dimaib/Pulse_bracelet/braslet/schematic&pcb/Корпуса/Корпус_103new/плата.SLDPRT

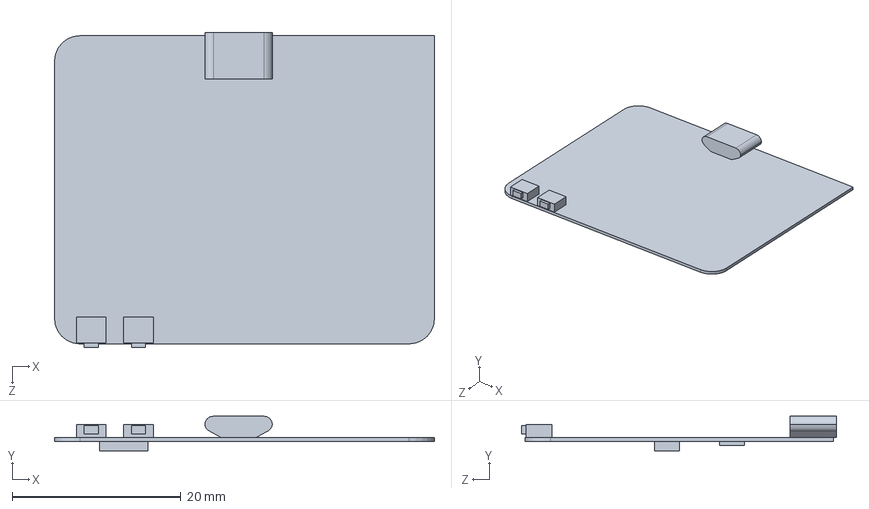
[picture p17: CAD file, 2022-04-17]
braslet/schematic&pcb/Корпуса/Корпус_103new/плата.SLDPRT
45.0 x 4.10 x 37.2 mm
