dimaib/Pulse_bracelet/Prog/body_temp_103new_optimized/Inc/hello.h

#ifndef HELLO_H
#define HELLO_H
#include "main.h"

//uint32_t foo_size=4364;

char foo[] = {
  0x80, 0x7f, 0x80, 0x7f, 0x80, 0x7f, 0x80, 0x7f, 
  0x80, 0x7f, 0x80, 0x7f, 0x80, 0x80, 0x80, 0x81, 
  0x81, 0x80, 0x81, 0x81, 0x7f, 0x80, 0x80, 0x80, 
  0x80, 0x7f, 0x80, 0x80, 0x7f, 0x7f, 0x7f, 0x7f, 
  0x7f, 0x7e, 0x7f, 0x7f, 0x7f, 0x7f, 0x80, 0x80, 
  0x80, 0x80, 0x7f, 0x81, 0x80, 0x81, 0x81, 0x80, 
  0x80, 0x80, 0x82, 0x82, 0x80, 0x80, 0x7f, 0x80, 
  0x7f, 0x7e, 0x7e, 0x7d, 0x7e, 0x7e, 0x7e, 0x7d, 
  0x7c, 0x7d, 0x7e, 0x7f, 0x7e, 0x7f, 0x7f, 0x80, 
  0x7f, 0x80, 0x80, 0x80, 0x80, 0x7f, 0x80, 0x7f, 
  0x7e, 0x7f, 0x7e, 0x7c, 0x7e, 0x7f, 0x7e, 0x7d, 
  0x7c, 0x7e, 0x7e, 0x7d, 0x7c, 0x7d, 0x7d, 0x7d, 
  0x7c, 0x7d, 0x7d, 0x7d, 0x7e, 0x80, 0x82, 0x84, 
  0x86, 0x87, 0x89, 0x8b, 0x8a, 0x89, 0x88, 0x86, 
  0x84, 0x80, 0x7e, 0x7e, 0x7b, 0x79, 0x79, 0x79, 
  0x7a, 0x7a, 0x7b, 0x7b, 0x7c, 0x7b, 0x7c, 0x7c, 
  0x7a, 0x7a, 0x79, 0x79, 0x79, 0x7a, 0x79, 0x7a, 
  0x7f, 0x85, 0x88, 0x8a, 0x90, 0x94, 0x96, 0x94, 
  0x91, 0x91, 0x8c, 0x85, 0x81, 0x7b, 0x78, 0x74, 
  0x71, 0x72, 0x72, 0x76, 0x77, 0x78, 0x7c, 0x7c, 
  0x7d, 0x7d, 0x7b, 0x7a, 0x79, 0x77, 0x76, 0x75, 
  0x75, 0x76, 0x76, 0x7d, 0x88, 0x89, 0x8e, 0x98, 
  0x9b, 0x9e, 0x9c, 0x98, 0x96, 0x8f, 0x84, 0x7e, 
  0x77, 0x71, 0x6d, 0x6b, 0x6c, 0x6e, 0x73, 0x76, 
  0x7b, 0x7d, 0x7f, 0x80, 0x7f, 0x7f, 0x7c, 0x7a, 
  0x77, 0x75, 0x73, 0x73, 0x74, 0x73, 0x7c, 0x88, 
  0x88, 0x8f, 0x9a, 0x9d, 0x9f, 0x9e, 0x9a, 0x99, 
  0x90, 0x85, 0x7f, 0x78, 0x70, 0x6d, 0x6a, 0x6b, 
  0x6e, 0x71, 0x76, 0x7a, 0x7c, 0x7f, 0x7f, 0x7f, 
  0x7e, 0x7b, 0x7a, 0x76, 0x75, 0x74, 0x73, 0x74, 
  0x73, 0x7b, 0x85, 0x85, 0x8c, 0x97, 0x99, 0x9c, 
  0x9c, 0x9a, 0x99, 0x92, 0x89, 0x84, 0x7e, 0x77, 
  0x73, 0x70, 0x70, 0x6f, 0x71, 0x74, 0x75, 0x78, 
  0x79, 0x7b, 0x7c, 0x79, 0x79, 0x78, 0x76, 0x76, 
  0x74, 0x75, 0x76, 0x74, 0x7a, 0x81, 0x83, 0x88, 
  0x8f, 0x95, 0x97, 0x97, 0x98, 0x98, 0x93, 0x8e, 
  0x89, 0x84, 0x80, 0x7b, 0x79, 0x78, 0x76, 0x77, 
  0x76, 0x78, 0x78, 0x78, 0x79, 0x79, 0x79, 0x77, 
  0x77, 0x77, 0x76, 0x76, 0x76, 0x76, 0x76, 0x77, 
  0x7c, 0x80, 0x83, 0x87, 0x8c, 0x8f, 0x91, 0x91, 
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
};

#endif	//HELLO_H
