dimaib/Pulse_bracelet/Prog/body_temp_103new_optimized/Inc/wav_arr.h

static const char wav_ism_puls[] = {
  0x80, 0x7f, 0x7f, 0x7e, 0x7f, 0x80, 0x80, 0x7f, 
  0x80, 0x81, 0x81, 0x81, 0x82, 0x83, 0x82, 0x82, 
  0x83, 0x84, 0x83, 0x82, 0x82, 0x81, 0x80, 0x81, 
  0x80, 0x7f, 0x80, 0x7f, 0x80, 0x7f, 0x7f, 0x7f, 
  0x7f, 0x7f, 0x7f, 0x7e, 0x7f, 0x7f, 0x7f, 0x7f, 
  0x7e, 0x7f, 0x7e, 0x7f, 0x7e, 0x7f, 0x7e, 0x7f, 
  0x7f, 0x7f, 0x7f, 0x7e, 0x7f, 0x7e, 0x7f, 0x7e, 
  0x7e, 0x7f, 0x7e, 0x7e, 0x7f, 0x7e, 0x7f, 0x7e, 
  0x7e, 0x7f, 0x7e, 0x7f, 0x7e, 0x7d, 0x7e, 0x7e, 
  0x7f, 0x7f, 0x80, 0x81, 0x82, 0x82, 0x83, 0x83, 
  0x84, 0x85, 0x86, 0x85, 0x86, 0x85, 0x84, 0x84, 
  0x84, 0x83, 0x83, 0x82, 0x82, 0x81, 0x80, 0x80, 
  0x80, 0x80, 0x80, 0x80, 0x7f, 0x80, 0x7f, 0x80, 
  0x7f, 0x7e, 0x7f, 0x7e, 0x7f, 0x7e, 0x7e, 0x7d, 
  0x7e, 0x7d, 0x7e, 0x7d, 0x7d, 0x7e, 0x7d, 0x7d, 
  0x7d, 0x7c, 0x7d, 0x7c, 0x7d, 0x7d, 0x7c, 0x7d, 
  0x7c, 0x7d, 0x7c, 0x7d, 0x7d, 0x7c, 0x7c, 0x7c, 
  0x7c, 0x7c, 0x7c, 0x7b, 0x7c, 0x7d, 0x7f, 0x80, 
  0x80, 0x81, 0x82, 0x83, 0x84, 0x85, 0x86, 0x87, 
  0x88, 0x88, 0x87, 0x87, 0x86, 0x86, 0x86, 0x86, 
  0x85, 0x85, 0x84, 0x84, 0x83, 0x82, 0x82, 0x82, 
  0x82, 0x81, 0x81, 0x80, 0x7f, 0x80, 0x7f, 0x80, 
  0x7f, 0x7e, 0x7e, 0x7e, 0x7e, 0x7d, 0x7d, 0x7d, 
  0x7c, 0x7d, 0x7c, 0x7c, 0x7b, 0x7c, 0x7b, 0x7b, 
  0x7b, 0x7b, 0x7b, 0x7b, 0x7a, 0x7b, 0x7a, 0x7b, 
  0x7a, 0x7b, 0x7b, 0x7a, 0x7a, 0x7a, 0x7a, 0x7a, 
  0x79, 0x7a, 0x7a, 0x7b, 0x7c, 0x7e, 0x7f, 0x80, 
  0x80, 0x81, 0x83, 0x84, 0x86, 0x87, 0x88, 0x88, 
  0x89, 0x88, 0x89, 0x89, 0x89, 0x88, 0x89, 0x88, 
  0x88, 0x87, 0x87, 0x86, 0x86, 0x85, 0x84, 0x84, 
  0x83, 0x83, 0x82, 0x81, 0x81, 0x80, 0x80, 0x7f, 
  0x80, 0x7f, 0x7f, 0x7e, 0x7e, 0x7e, 0x7c, 0x7d, 
  0x7c, 0x7b, 0x7c, 0x7b, 0x7b, 0x7b, 0x7a, 0x7b, 
  0x7a, 0x7a, 0x7a, 0x79, 0x7a, 0x79, 0x79, 0x79, 
  0x79, 0x79, 0x79, 0x78, 0x79, 0x78, 0x79, 0x78, 
  0x79, 0x78, 0x79, 0x7a, 0x7c, 0x7e, 0x7f, 0x7f, 
  0x80, 0x81, 0x82, 0x84, 0x86, 0x87, 0x88, 0x88, 
  0x89, 0x88, 0x89, 0x8a, 0x89, 0x8a, 0x89, 0x89, 
  0x89, 0x88, 0x87, 0x87, 0x86, 0x86, 0x85, 0x84, 
  0x84, 0x83, 0x82, 0x81, 0x81, 0x80, 0x80, 0x7f, 
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
};
