dimaib/Pulse_bracelet/Prog/body_temp_103new_optimized/Inc/spx.h

#include "main.h"

#ifndef SPX_H
#define SPX_H
unsigned int spx_size=1248;
const uint16_t spx_frames2=62;

const uint8_t spx_voice2[] = {
  0x88, 0x0e, 0x73, 0x9d, 0xb4, 0x07, 0x39, 0xce, 
  0x1e, 0x9d, 0x66, 0x0f, 0xc0, 0x39, 0xce, 0x70, 
  0x00, 0x1c, 0xe7, 0x38, 0x10, 0x0e, 0x73, 0x9c, 
  0x00, 0x07, 0x39, 0xce, 0x1e, 0x9d, 0x66, 0x00, 
  0x00, 0x39, 0xce, 0x70, 0x00, 0x1c, 0xe7, 0x38, 
  0x00, 0x0e, 0x73, 0x9c, 0x00, 0x07, 0x39, 0xce, 
  0x1e, 0x9d, 0x66, 0x00, 0x00, 0x39, 0xce, 0x70, 
  0x00, 0x1c, 0xe7, 0x38, 0x00, 0x0e, 0x73, 0x9c, 
  0x00, 0x07, 0x39, 0xce, 0x1e, 0x9d, 0x66, 0x00, 
  0x00, 0x39, 0xce, 0x70, 0x00, 0x1c, 0xe7, 0x38, 
  0x00, 0x0e, 0x73, 0x9c, 0x00, 0x07, 0x39, 0xce, 
  0x1e, 0x9d, 0x66, 0x00, 0x00, 0x39, 0xce, 0x70, 
  0x00, 0x1c, 0xe7, 0x38, 0x00, 0x0e, 0x73, 0x9c, 
  0x00, 0x07, 0x39, 0xce, 0x1e, 0x9d, 0x66, 0x00, 
  0x00, 0x39, 0xce, 0x70, 0x00, 0x1c, 0xe7, 0x38, 
  0x00, 0x0e, 0x73, 0x9c, 0x00, 0x07, 0x39, 0xce, 
  0x1e, 0x9d, 0x66, 0x00, 0x00, 0x39, 0xce, 0x70, 
  0x00, 0x1c, 0xe7, 0x38, 0x00, 0x0e, 0x73, 0x9c, 
  0x00, 0x07, 0x39, 0xce, 0x1e, 0x9d, 0x66, 0x00, 
  0x00, 0x39, 0xce, 0x70, 0x00, 0x1c, 0xe7, 0x38, 
  0x00, 0x0e, 0x73, 0x9c, 0x00, 0x07, 0x39, 0xce, 
  0x1e, 0x9d, 0x66, 0x00, 0x00, 0x39, 0xce, 0x70, 
  0x00, 0x1c, 0xe7, 0x38, 0x00, 0x0e, 0x73, 0x9c, 
  0x00, 0x07, 0x39, 0xce, 0x1c, 0x5f, 0xa8, 0x80, 
  0x40, 0x39, 0xce, 0x70, 0x90, 0x1c, 0xe7, 0x24, 
  0xbc, 0x9e, 0x55, 0xc4, 0x32, 0x19, 0x80, 0x16, 
  0x1c, 0x49, 0x43, 0x34, 0xb0, 0x3b, 0x90, 0xc8, 
  0xd8, 0x06, 0x5e, 0xa0, 0x67, 0x74, 0x6c, 0x98, 
  0xa2, 0x54, 0xdf, 0x78, 0x1c, 0x4c, 0x63, 0x71, 
  0x74, 0x37, 0x91, 0x70, 0xad, 0xda, 0xea, 0x38, 
  0x55, 0x81, 0xdb, 0xfc, 0x27, 0xbd, 0x4a, 0x90, 
  0x1e, 0x73, 0x31, 0x74, 0x98, 0xc7, 0x8e, 0x70, 
  0x95, 0x1a, 0x46, 0x58, 0x4d, 0x0f, 0x7b, 0x64, 
  0x8c, 0xcf, 0xaa, 0x59, 0x18, 0x7a, 0x31, 0x57, 
  0xcb, 0xed, 0xd3, 0xc0, 0xa9, 0xd2, 0xed, 0x4c, 
  0x52, 0xf6, 0xbb, 0x88, 0x2e, 0x65, 0x1b, 0x1c, 
  0x1f, 0x6b, 0x03, 0x31, 0x6e, 0x97, 0x59, 0x30, 
  0xcd, 0x7b, 0xa3, 0x74, 0x6b, 0xf6, 0x30, 0xc6, 
  0x36, 0xe0, 0x95, 0xa1, 0x1d, 0x6b, 0xf3, 0x11, 
  0xa6, 0xba, 0x4e, 0x32, 0xc9, 0xad, 0xda, 0xb0, 
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
};
 
#endif
