dimaib/Pulse_bracelet/Prog/body_temp_103new_optimized/Inc/filters.h

/*
 * filters.h
 *
 *  Created on: Oct 10, 2020
 *      Author: ivan
 */

#ifndef INC_FILTERS_H_
#define INC_FILTERS_H_

#include "hr_defines.h"
#include "arm_math.h"

/* ----------------------------------------------------------------------
** Filters' Coefficients buffer generated using MATLAB.
** ------------------------------------------------------------------- */

const float32_t HighPassDetrendingCoeffsF32[NUM_TAPS_DETRENDING*5] = {
  0.984206697730477f, -1.968413395460955f, 0.984206697730478f, 1.967592517263235f, -0.969234273658676f,
  0.963251495007389f, -1.926502990014779f, 0.963251495007389f, 1.925699589516696f, -0.927306390512861f
};

const float32_t LowPassSmoothingCoeffsF32[NUM_TAPS_SMOOTHING*5] = {
		 0.603354646433095f, -1.188565352593063f, 0.603354646433095f, 1.970883379669074f, -0.99082003727772f,
		 0.661784321313225f, -1.291887217173096f, 0.661784321313225f, 1.962070672464945f, -0.97481945829969f,
		 0.280045409706732f, -1.725871961934199f, 0.280045409706732f, 1.950161187192124f, -0.95283541274852f,
		 0.009311752655434f, -0.018377197915566f, 0.009311752655434f, 1.975284172938610f, -0.99787210529172f
};

const float32_t LowPassDerivativeCoeffsF32[NUM_TAPS_DERIVATIVE] = {
		-0.000614763152435f	,
		 0.004094511116178f	,
		 0.008325954918809f	,
		 0.015493746864750f ,
		 0.025337018066656f	,
		 0.037578941827889f	,
		 0.051580808183620f	,
		 0.066326164207601f	,
		 0.080525506875535f	,
		 0.092786135694162f	,
		 0.101810691193580f	,
		 0.106596358286361f	,
		 0.106596358286361f	,
		 0.101810691193581f	,
		 0.092786135694163f	,
		 0.080525506875535f	,
		 0.066326164207601f	,
		 0.051580808183621f	,
		 0.037578941827889f	,
		 0.025337018066656f	,
		 0.015493746864751f	,
		 0.008325954918809f	,
		 0.004094511116178f	,
		-0.000614763152435f
};


#endif /* INC_FILTERS_H_ */
