dimaib/Pulse_bracelet/Prog/body_temp_103new_optimized/Inc/hr_spo2_math.h

#ifndef HR_SPO2_MATH_H
#define HR_SPO2_MATH_H
#include "main.h"
#include "arm_math.h"
#include "hr_defines.h"

void hr_math_(float32_t *testInputR, float32_t *testInputIR);
void hr_filter_init();

#endif //HR_SPO2_MATH_H
