dimaib/Pulse_bracelet/Prog/body_temp_103new_optimized/Inc/samples.h

#ifndef INC_SAMPLES_H_
#define INC_SAMPLES_H_

#include "arm_math.h"
#include "hr_defines.h"

/* ----------------------------------------------------------------------
** Test input signal contains 1000Hz + 15000 Hz
** ------------------------------------------------------------------- */

float32_t testInputIR[TEST_LENGTH_SAMPLES] =
{
33388	,
33360	,
33368	,
33364	,
33388	,
33372	,
33356	,
33380	,
33380	,
33372	,
33376	,
33388	,
33388	,
33360	,
33368	,
33388	,
33372	,
33356	,
33348	,
33344	,
33344	,
33356	,
33348	,
33344	,
33356	,
33336	,
33340	,
33336	,
33312	,
33320	,
33316	,
33320	,
33316	,
33300	,
33296	,
33292	,
33300	,
33280	,
33292	,
33284	,
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
};

float32_t testInputR[TEST_LENGTH_SAMPLES] =
{
27360	,
27368	,
27368	,
27356	,
27352	,
27372	,
27340	,
27356	,
27376	,
27364	,
27356	,
27344	,
27352	,
27332	,
27348	,
27364	,
27356	,
27336	,
27340	,
27328	,
27332	,
27340	,
27328	,
27312	,
27328	,
27312	,
27312	,
27312	,
27328	,
27304	,
27304	,
27312	,
27300	,
27280	,
27276	,
27288	,
27292	,
27284	,
27280	,
27280	,
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
};

#endif /* INC_SAMPLES_H_ */
